aditocco2/the_grad_pill/python/media_slideshow/2Frames.gif

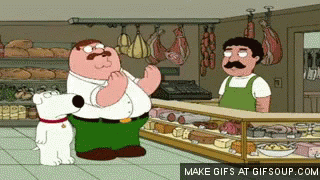
python/media_slideshow/2Frames.gif
