aditocco2/the_grad_pill/python/media_slideshow/all a man need fr.png

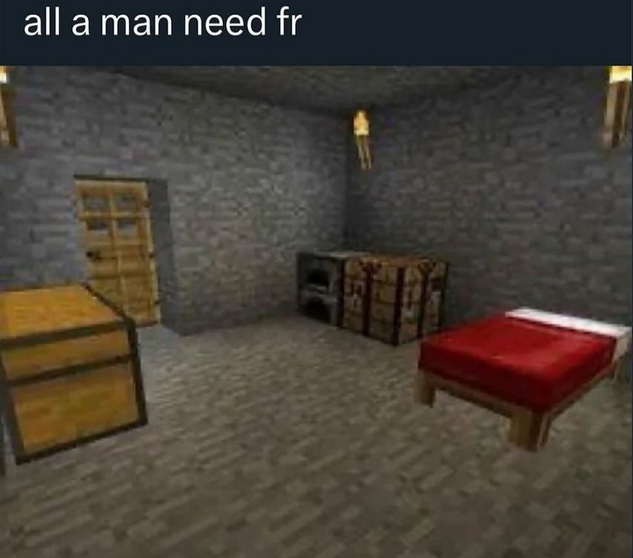
python/media_slideshow/all a man need fr.png
