aditocco2/the_grad_pill/python/media_slideshow/chicken villager.jpg

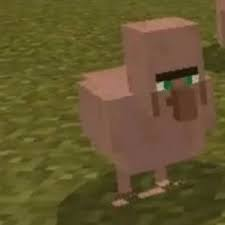
python/media_slideshow/chicken villager.jpg
