aditocco2/the_grad_pill/python/media_slideshow/goog.jpg

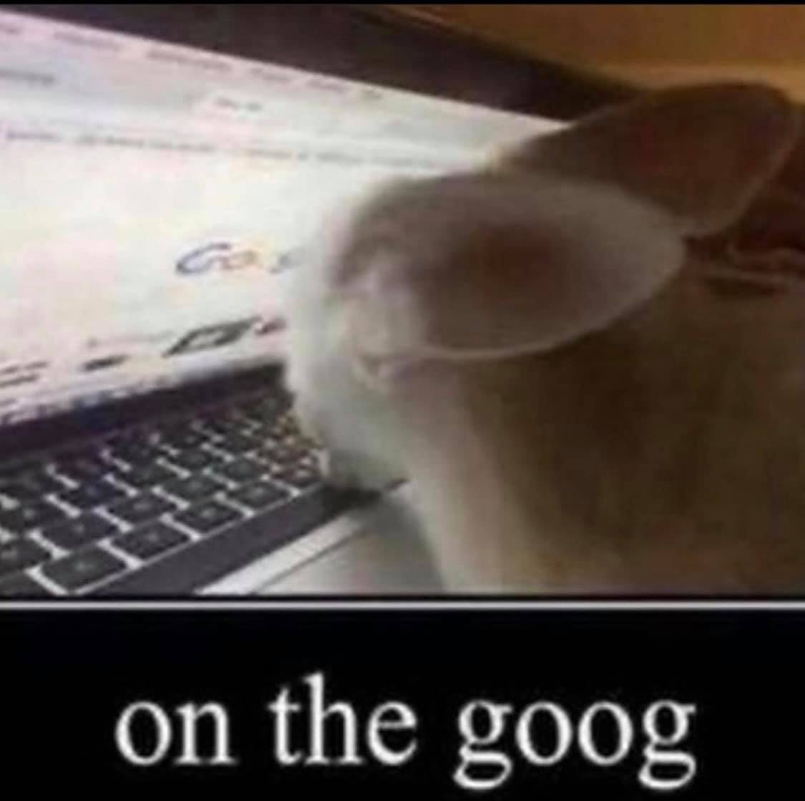
python/media_slideshow/goog.jpg
