aditocco2/the_grad_pill/python/media_slideshow/hands.jpg

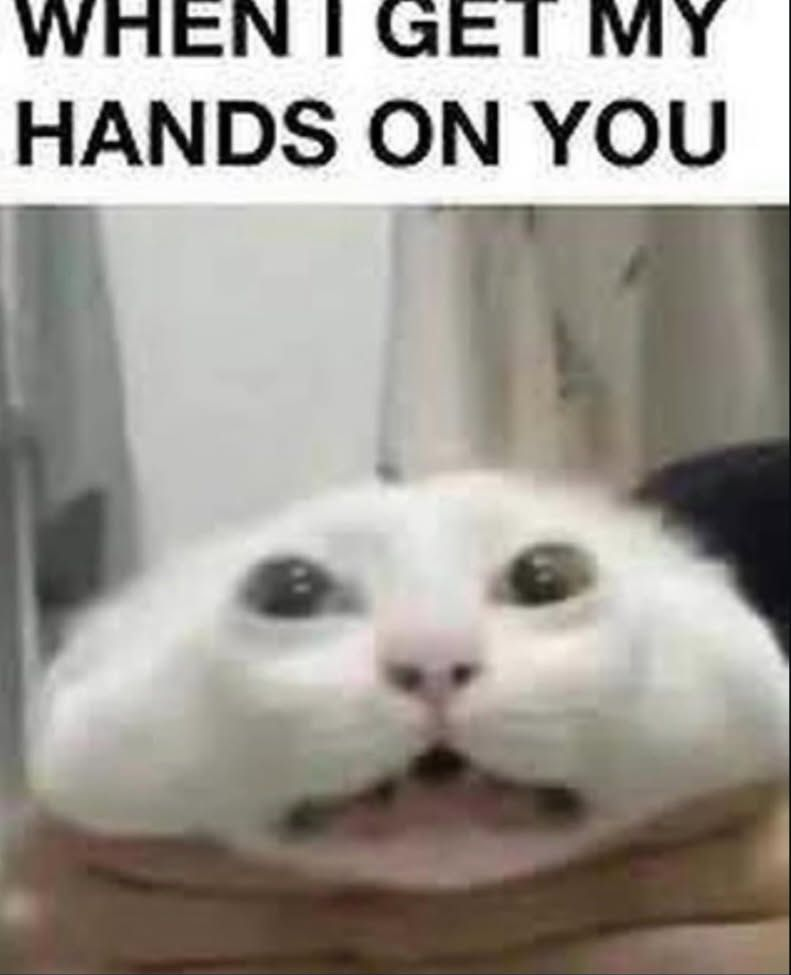
python/media_slideshow/hands.jpg
