aditocco2/the_grad_pill/python/media_slideshow/holy fucking shit 2019 was 5 years ago.png

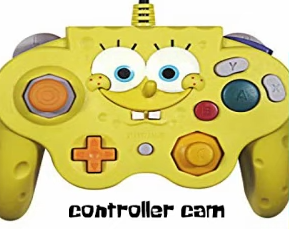
python/media_slideshow/holy fucking shit 2019 was 5 years ago.png
