aditocco2/the_grad_pill/python/media_slideshow/huell.gif

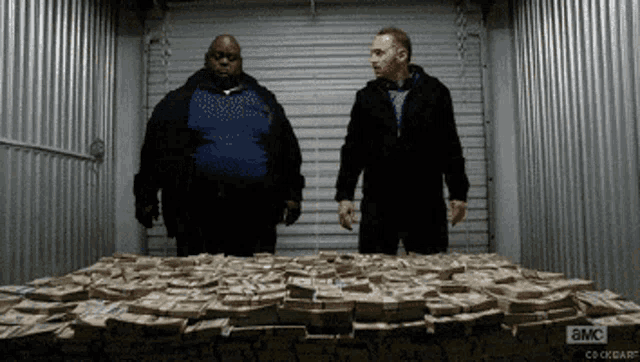
python/media_slideshow/huell.gif
