aditocco2/the_grad_pill/python/media_slideshow/lagoon trigger.png

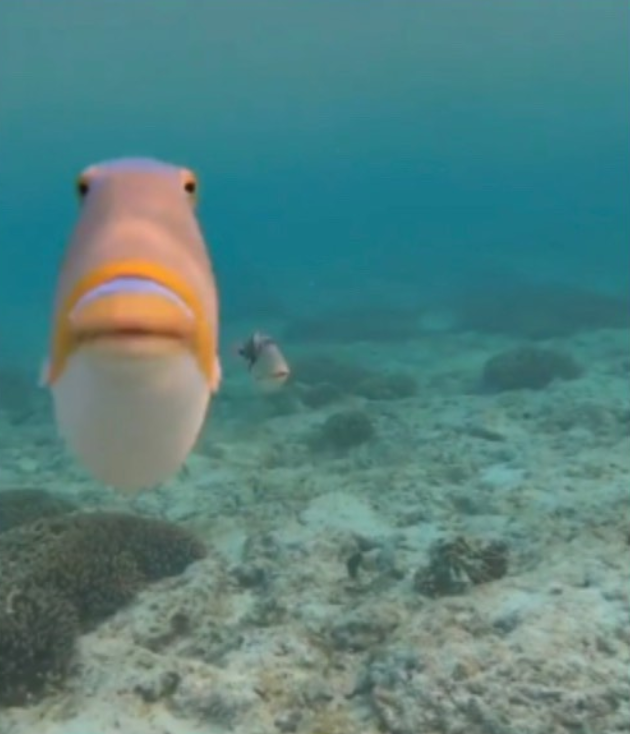
python/media_slideshow/lagoon trigger.png
