aditocco2/the_grad_pill/python/media_slideshow/man.jpg

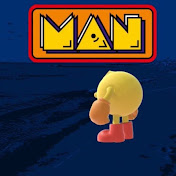
python/media_slideshow/man.jpg
