aditocco2/the_grad_pill/python/media_slideshow/numb.png

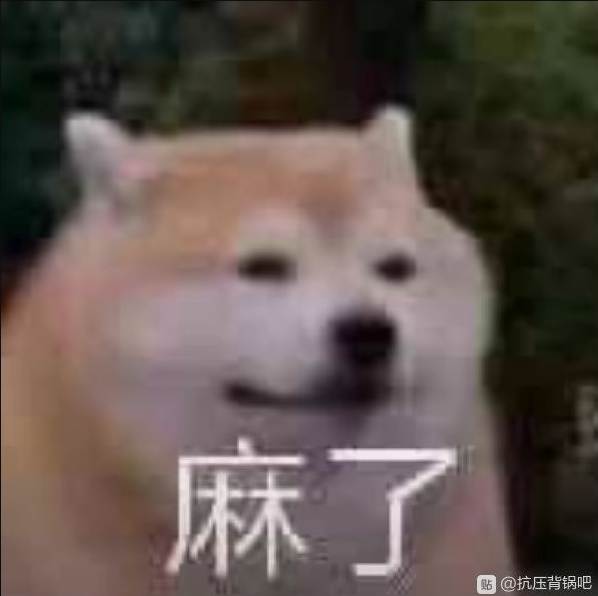
python/media_slideshow/numb.png
