aditocco2/the_grad_pill/python/media_slideshow/patriot.jpg

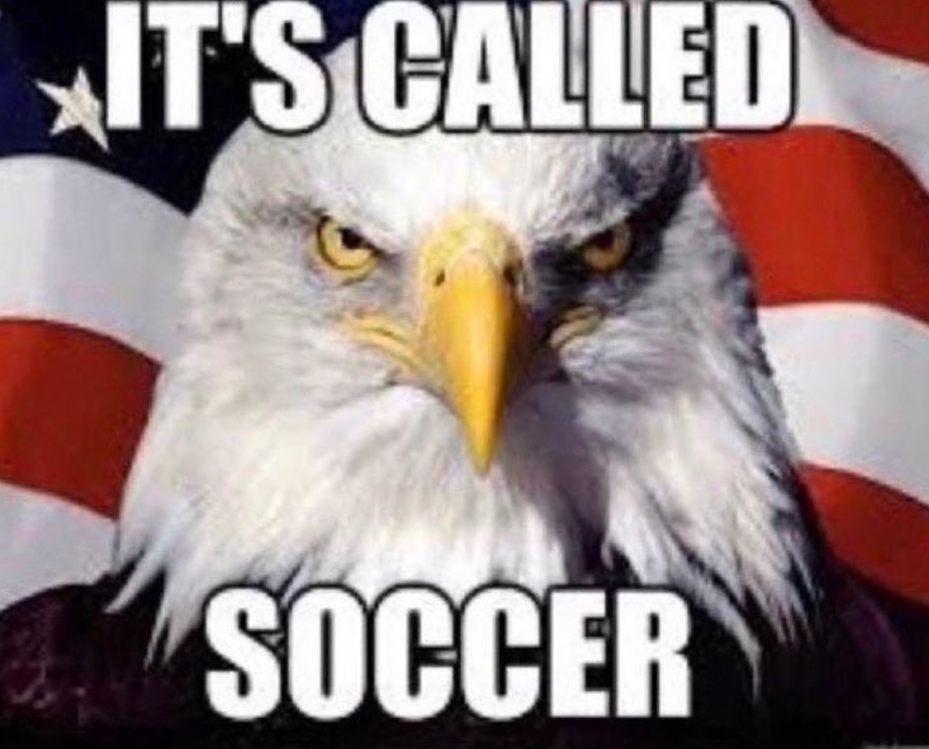
python/media_slideshow/patriot.jpg
