aditocco2/the_grad_pill/python/media_slideshow/petar.png

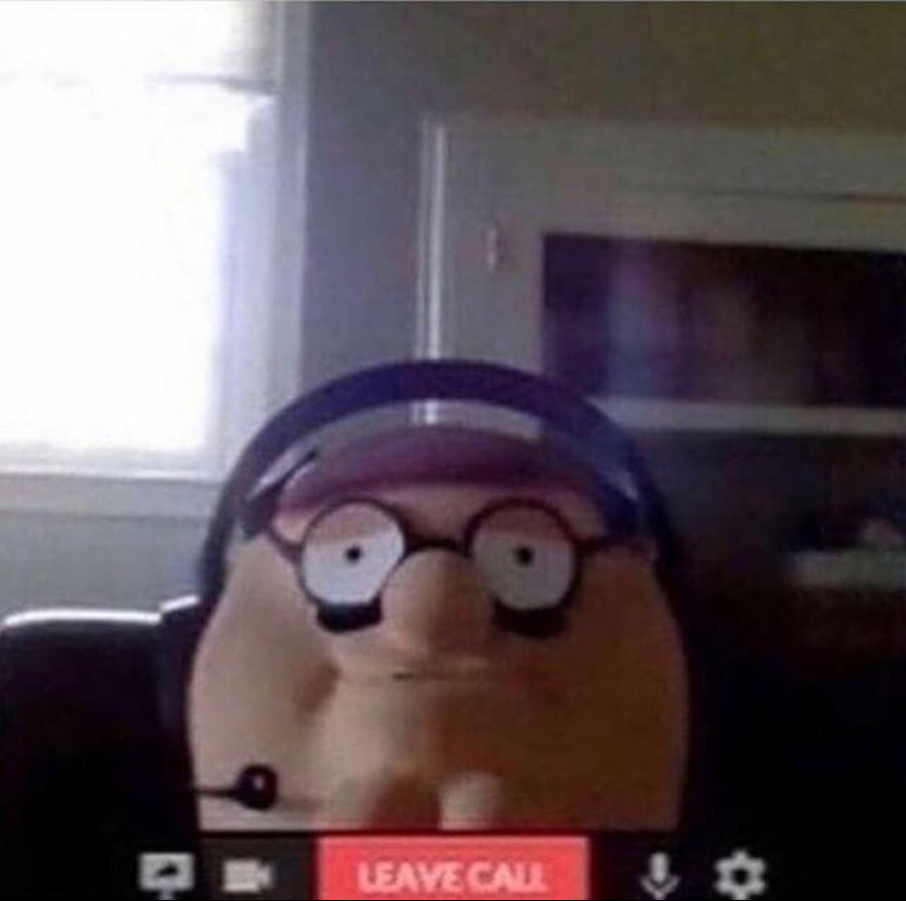
python/media_slideshow/petar.png
