aditocco2/the_grad_pill/python/media_slideshow/pitbull.jpg

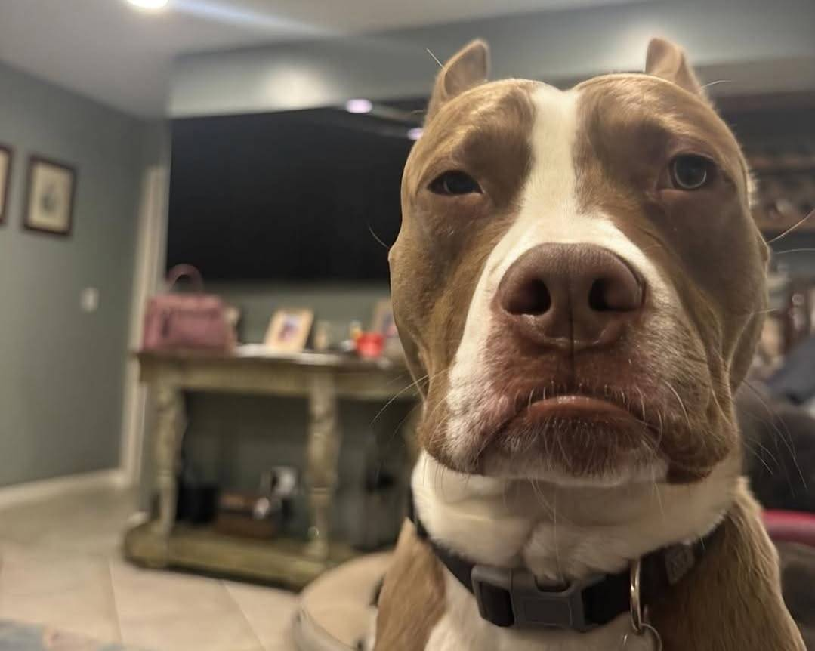
python/media_slideshow/pitbull.jpg
