aditocco2/the_grad_pill/python/media_slideshow/saul.gif

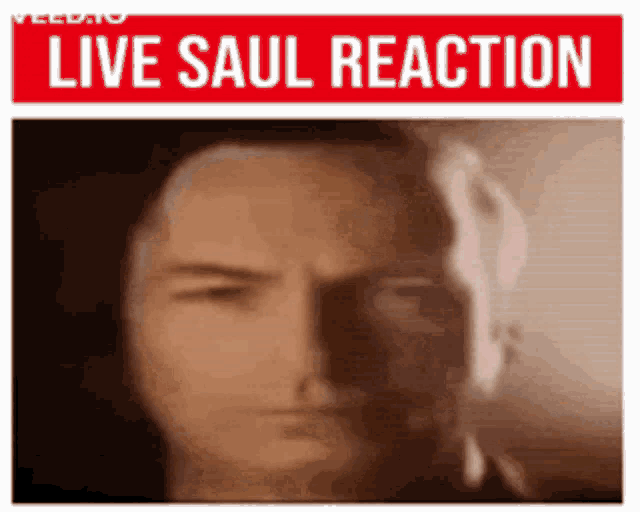
python/media_slideshow/saul.gif
