aditocco2/the_grad_pill/python/media_slideshow/shoe it to em.jpg

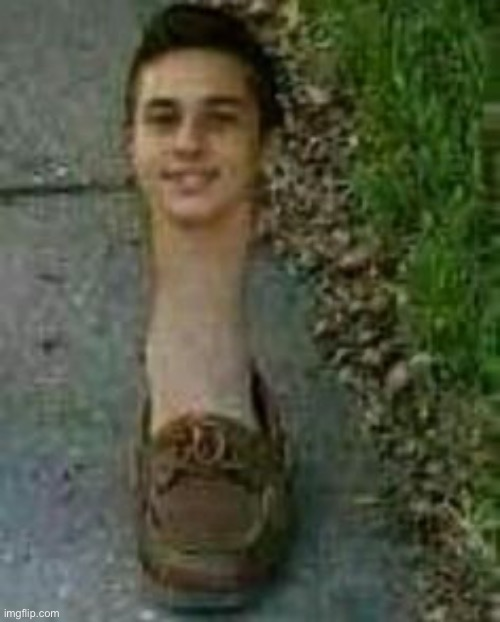
python/media_slideshow/shoe it to em.jpg
