aditocco2/the_grad_pill/python/media_slideshow/WawaCalling.jpg

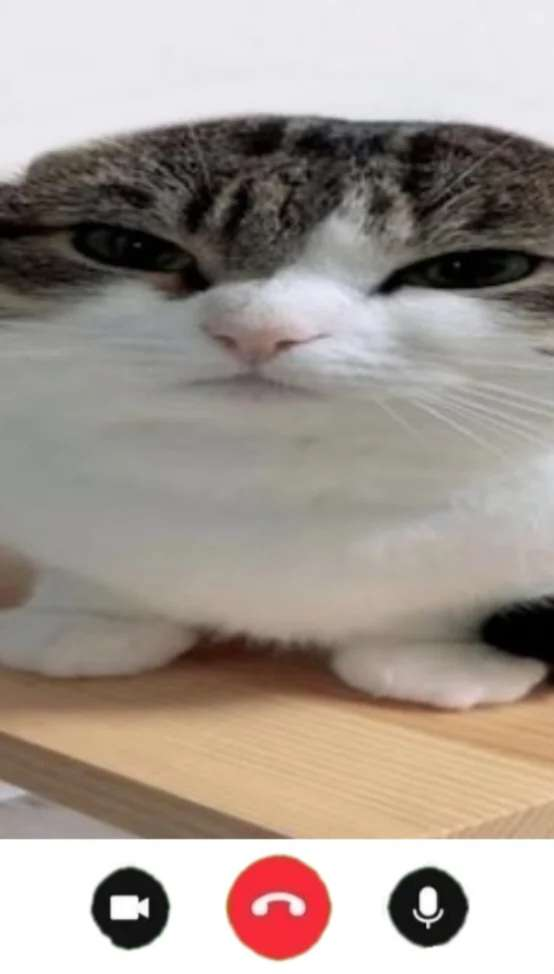
python/media_slideshow/WawaCalling.jpg
