aditocco2/the_grad_pill/pico/drivers/hub75_fonts.h

#ifndef HUB75_FONTS_H
#define HUB75_FONTS_H

#include <stdint.h>

// 4x6 pixel font by me, with inspiration from below:
// https://grid-paint.com/images/details/6312486409076736
const uint8_t small_font[96 * 6] = {
	0x00,0x00,0x00,0x00,0x00,0x00, //  
	0x04,0x04,0x04,0x00,0x04,0x00, // !
	0x0a,0x0a,0x00,0x00,0x00,0x00, // "
	0x0a,0x0e,0x0a,0x0e,0x0a,0x00, // #
	0x06,0x0c,0x04,0x06,0x0c,0x00, // $
	0x0a,0x02,0x04,0x08,0x0a,0x00, // %
	0x0c,0x0c,0x06,0x0a,0x06,0x00, // &
	0x08,0x08,0x00,0x00,0x00,0x00, // '
	0x02,0x04,0x04,0x04,0x02,0x00, // (
	0x08,0x04,0x04,0x04,0x08,0x00, // )
	0x00,0x0a,0x04,0x0a,0x00,0x00, // *
	0x00,0x04,0x0e,0x04,0x00,0x00, // +
	0x00,0x00,0x00,0x08,0x08,0x00, // ,
	0x00,0x00,0x0e,0x00,0x00,0x00, // -
	0x00,0x00,0x00,0x00,0x08,0x00, // .
	0x02,0x02,0x04,0x08,0x08,0x00, // /
	0x04,0x0a,0x0a,0x0a,0x04,0x00, // 0
	0x04,0x0c,0x04,0x04,0x0e,0x00, // 1
	0x0c,0x02,0x04,0x08,0x0e,0x00, // 2
	0x0c,0x02,0x06,0x02,0x0c,0x00, // 3
	0x08,0x0a,0x0e,0x02,0x02,0x00, // 4
	0x0e,0x08,0x0e,0x02,0x0c,0x00, // 5
	0x06,0x08,0x0e,0x0a,0x0e,0x00, // 6
	0x0e,0x02,0x04,0x08,0x08,0x00, // 7
	0x0e,0x0a,0x0e,0x0a,0x0e,0x00, // 8
	0x0e,0x0a,0x0e,0x02,0x0c,0x00, // 9
	0x00,0x04,0x00,0x04,0x00,0x00, // :
	0x00,0x04,0x00,0x04,0x04,0x00, // ;
	0x06,0x04,0x0c,0x04,0x06,0x00, // <
	0x00,0x0e,0x00,0x0e,0x00,0x00, // =
	0x0c,0x04,0x06,0x04,0x0c,0x00, // >
	0x0e,0x02,0x04,0x00,0x04,0x00, // ?
	0x04,0x0a,0x0a,0x08,0x06,0x00, // @
	0x0e,0x0a,0x0e,0x0a,0x0a,0x00, // A
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
	0x00,0x00,0x00,0xc0,0xe0,0x70,0x38,0x1c,0x38,0x70,0xe0,0xc0,0x00,0x00,0x00,0x00, // >
	0x00,0x00,0x78,0xfc,0xcc,0xcc,0x18,0x18,0x30,0x30,0x30,0x00,0x30,0x30,0x00,0x00, // ?
	0x00,0x00,0x70,0xf8,0xcc,0x84,0xb4,0xac,0xac,0xb8,0x80,0xc4,0xfc,0x78,0x00,0x00, // @
	0x00,0x00,0x30,0x78,0xfc,0xcc,0xcc,0xcc,0xfc,0xfc,0xcc,0xcc,0xcc,0xcc,0x00,0x00, // A
	0x00,0x00,0xf8,0xfc,0xcc,0xcc,0xfc,0xf8,0xcc,0xcc,0xcc,0xcc,0xfc,0xf8,0x00,0x00, // B
	0x00,0x00,0x78,0xfc,0xcc,0xcc,0xc0,0xc0,0xc0,0xc0,0xcc,0xcc,0xfc,0x78,0x00,0x00, // C
	0x00,0x00,0xf0,0xf8,0xdc,0xcc,0xcc,0xcc,0xcc,0xcc,0xcc,0xdc,0xf8,0xf0,0x00,0x00, // D
	0x00,0x00,0xfc,0xfc,0xc0,0xc0,0xf8,0xf8,0xc0,0xc0,0xc0,0xc0,0xfc,0xfc,0x00,0x00, // E
	0x00,0x00,0xfc,0xfc,0xc0,0xc0,0xf8,0xf8,0xc0,0xc0,0xc0,0xc0,0xc0,0xc0,0x00,0x00, // F
	0x00,0x00,0x7c,0xfc,0xc0,0xc0,0xdc,0xdc,0xcc,0xcc,0xcc,0xcc,0xfc,0x78,0x00,0x00, // G
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
};

#endif
